mahirsuljic-fet/PSoC-Projekat/slike/20260106_085644.jpg

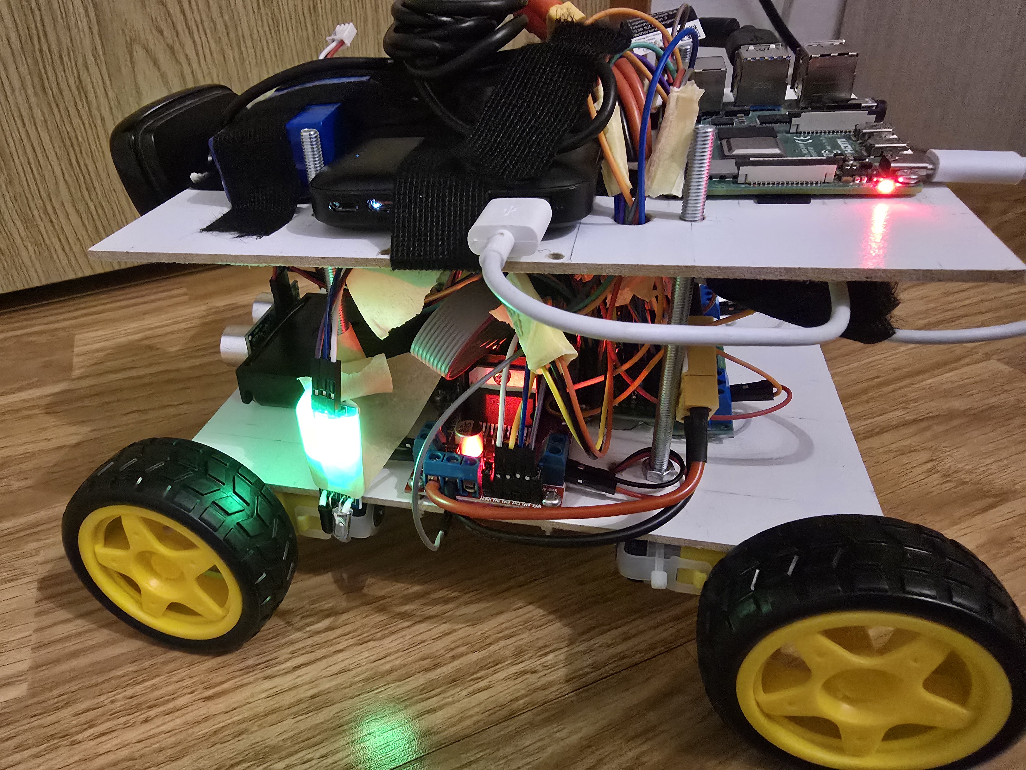
slike/20260106_085644.jpg
