mahirsuljic-fet/PSoC-Projekat/slike/20260106_085714.jpg

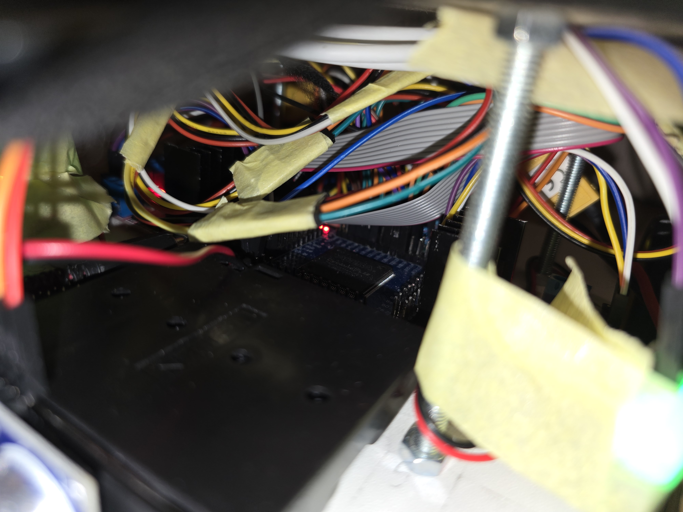
slike/20260106_085714.jpg
