mahirsuljic-fet/PSoC-Projekat/slike/left_motor.png

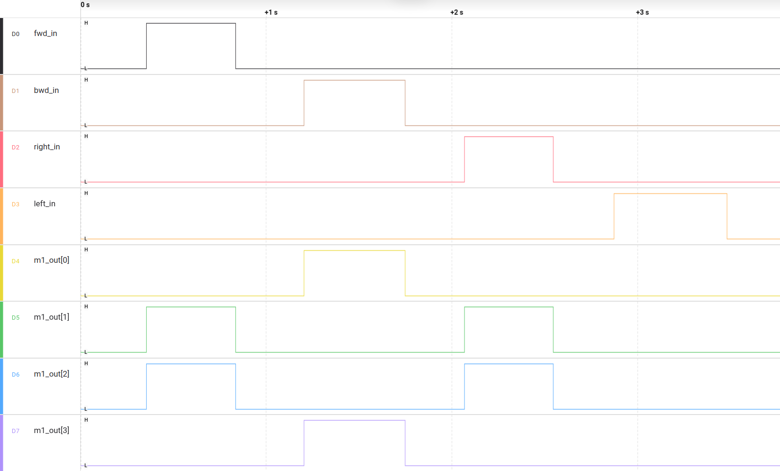
slike/left_motor.png
