mahirsuljic-fet/PSoC-Projekat/slike/line_detector.png

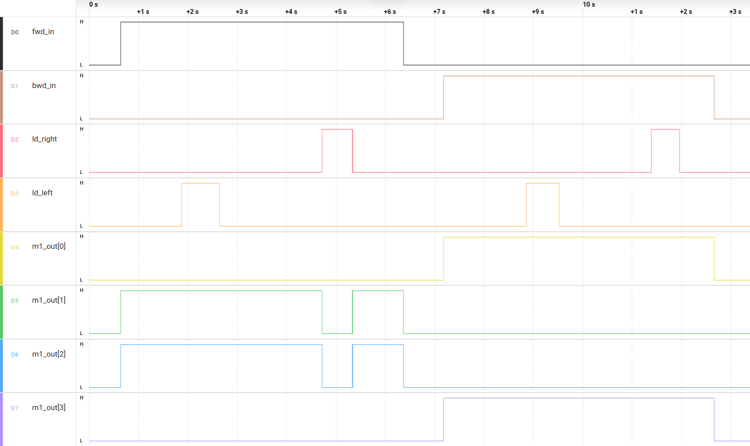
slike/line_detector.png
