mahirsuljic-fet/PSoC-Projekat/slike/ultrasonic_1.png

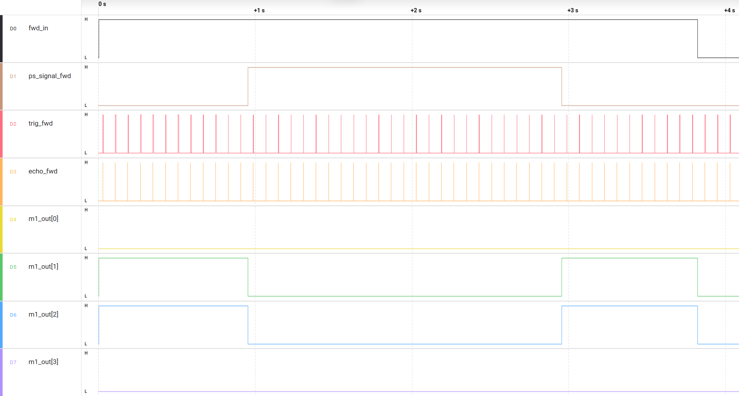
slike/ultrasonic_1.png
