mahirsuljic-fet/PSoC-Projekat/slike/ultrasonic_stop.png

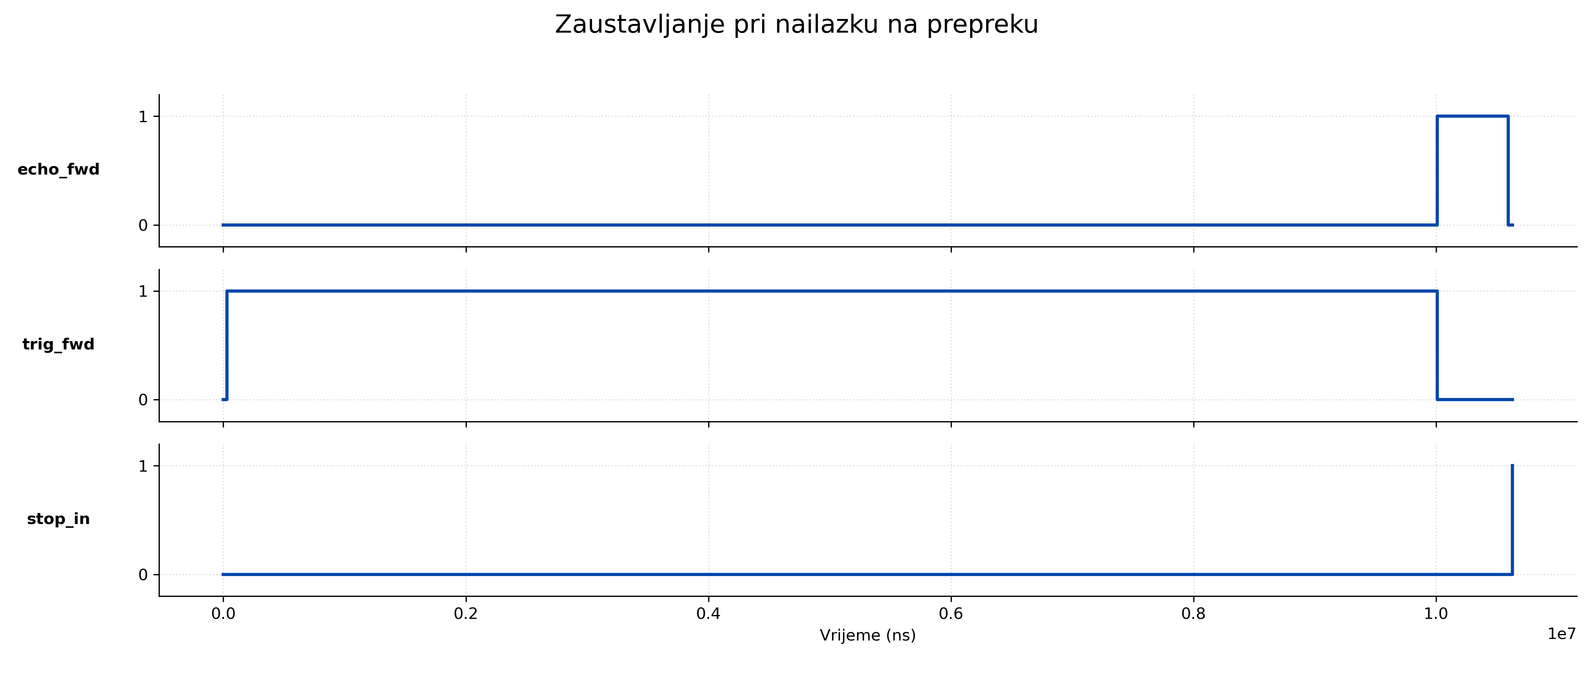
slike/ultrasonic_stop.png
