mahirsuljic-fet/PSoC-Projekat/slike/line_test.png

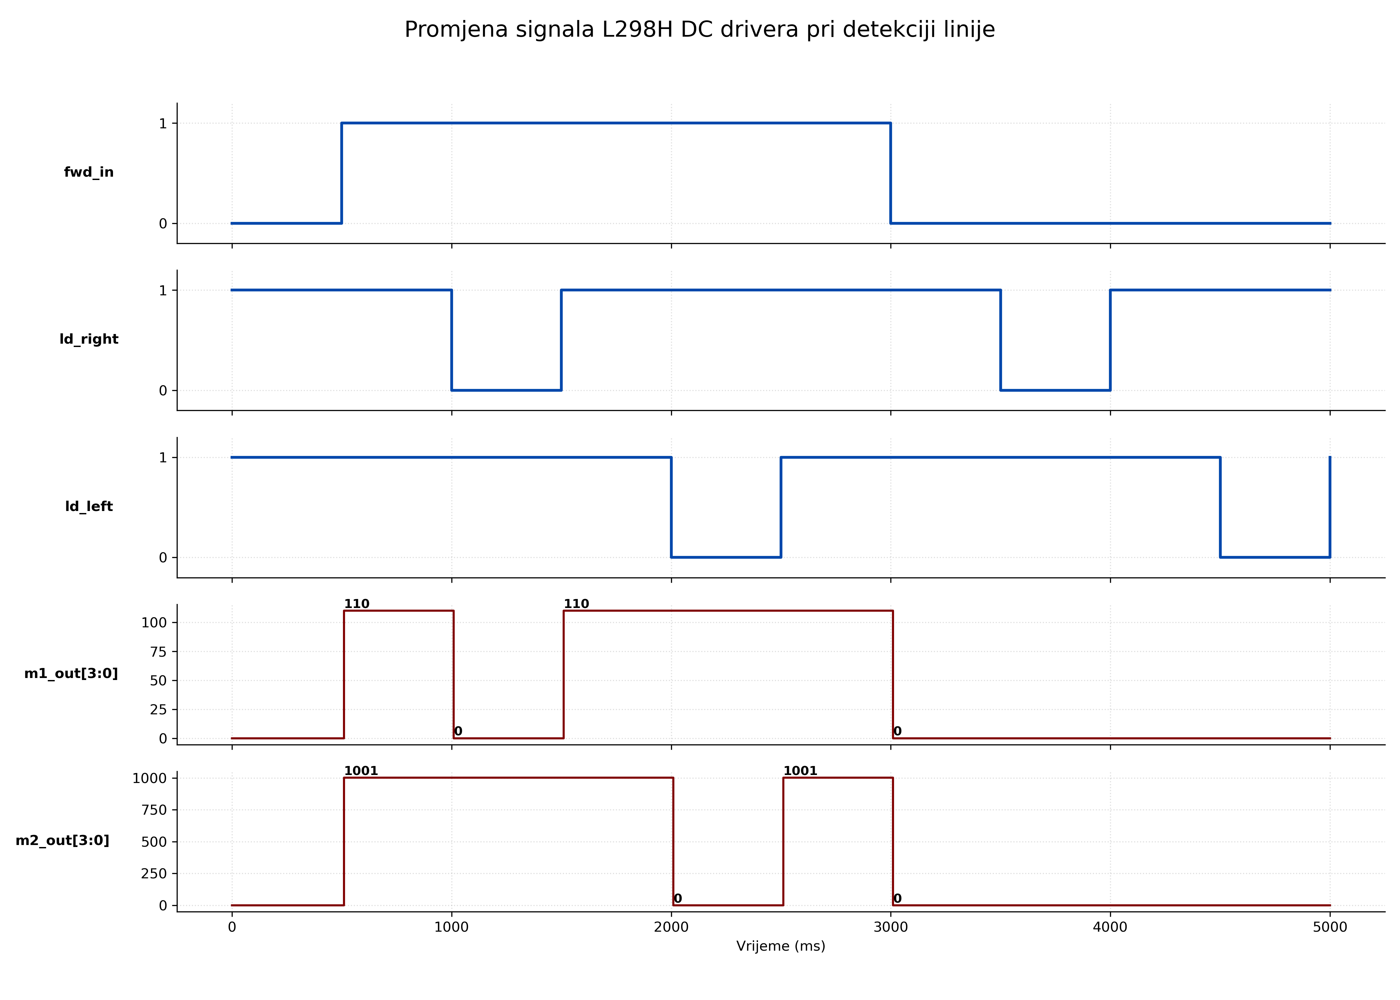
slike/line_test.png
