mahirsuljic-fet/PSoC-Projekat/slike/movement_test.png

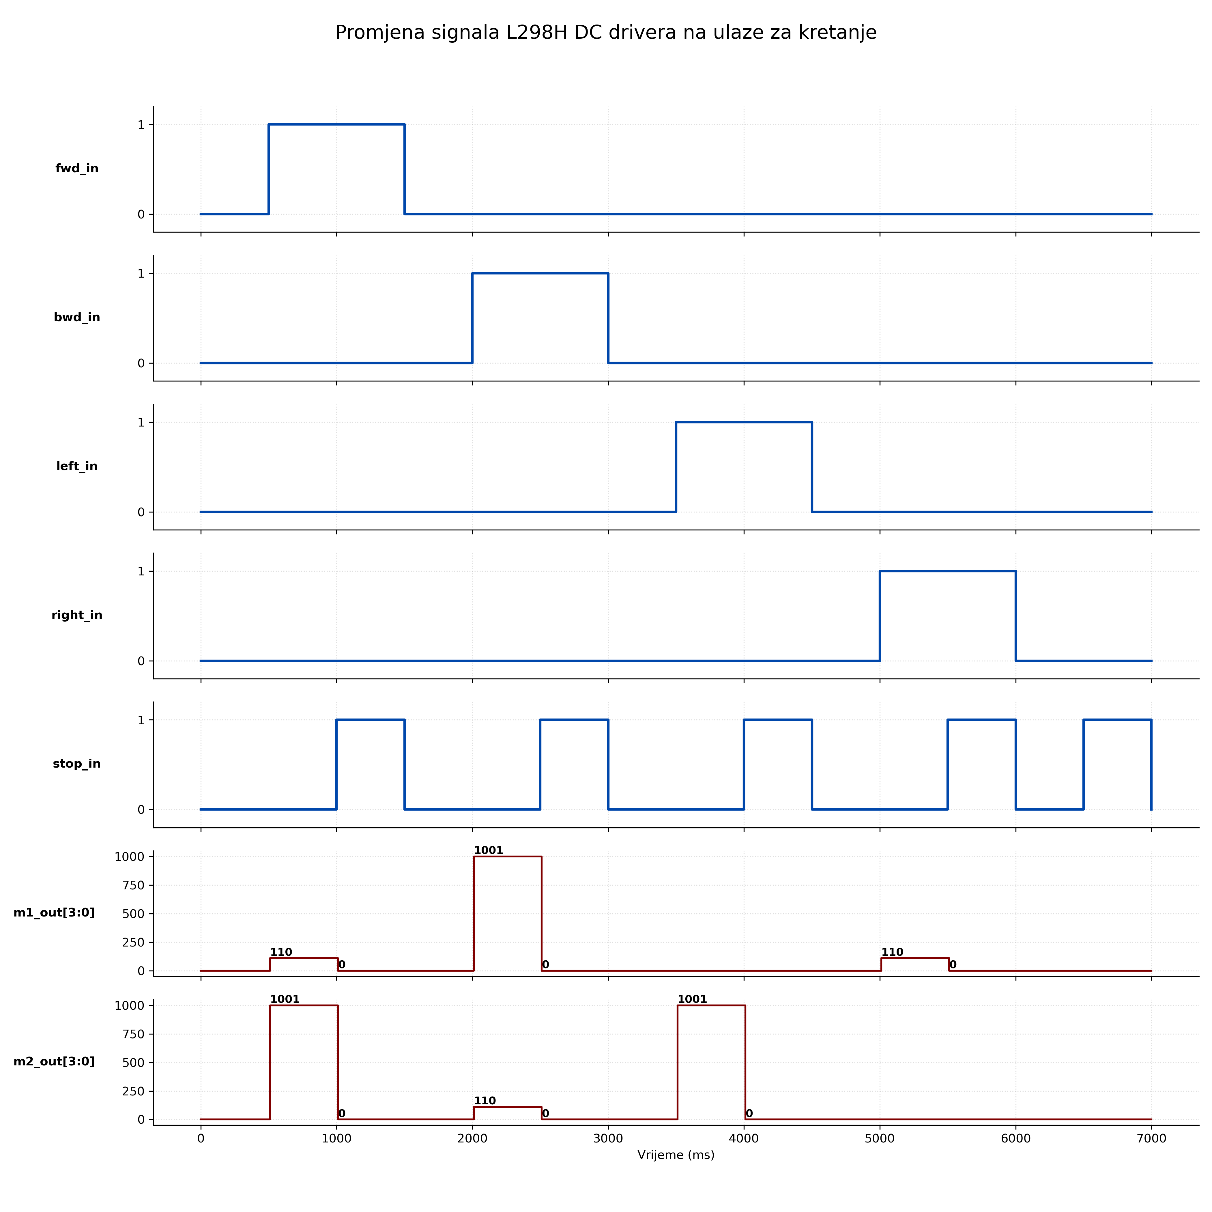
slike/movement_test.png
